christopherdacc/Projet_EEA0601/Compte_rendu/Finale/Présentation_Errard_Daccache.pdf

# Projet : Robot suiveur de ligne

MODULE EEA 0601

TP TRANSDISCIPLINAIRE ANNÉE 2023/2024

1

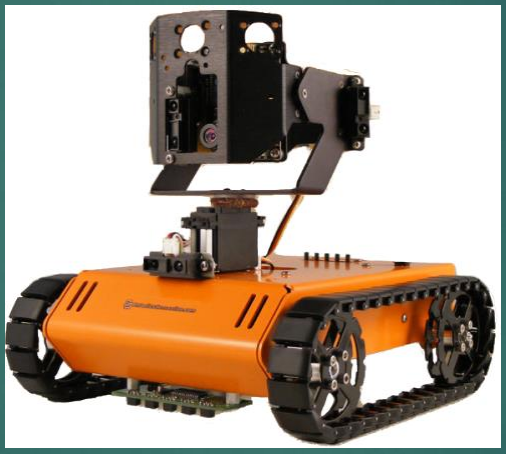
[picture p47: figure]

Sujet : Interface Homme Machine d’un Robot Suiveur de Ligne Réalisé par ERRARD Mathéo et DACCACHE Christopher Enseignants responsables : COLAS Maxime et CARTON David

2

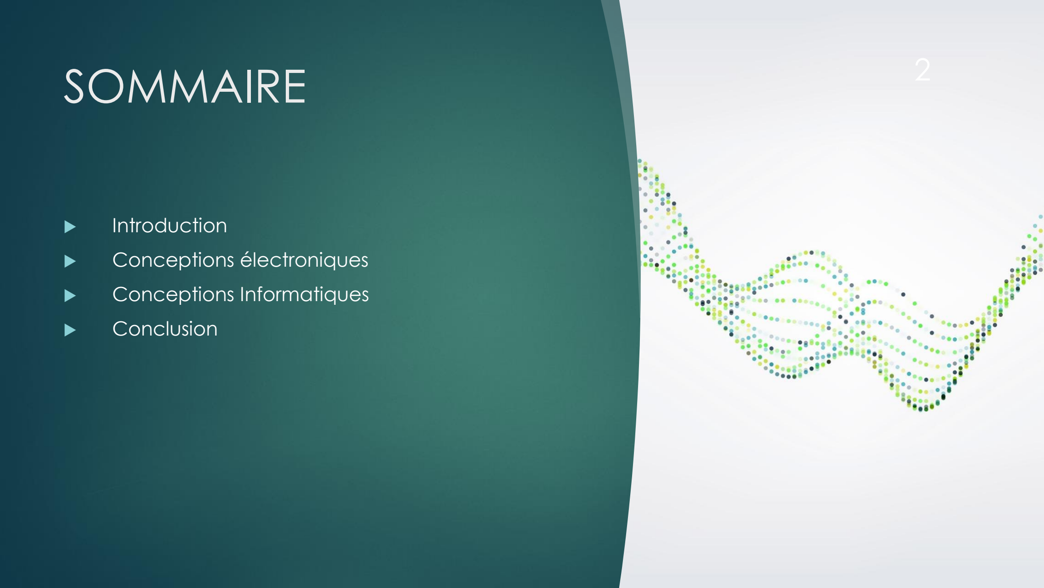
[picture p48: page 2]

SOMMAIRE | Introduction | Conceptions électroniques | Conceptions Informatiques | Conclusion

I. Introduction Cahier des charges Matériel Utilisé
3

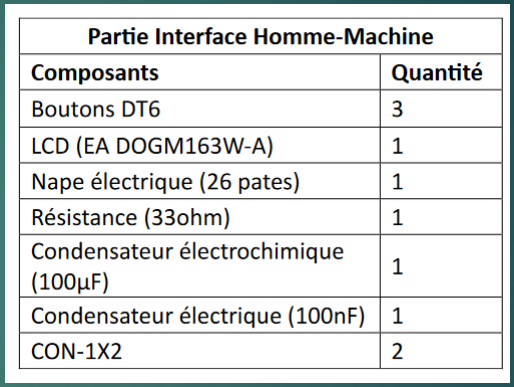
[picture p49: figure]
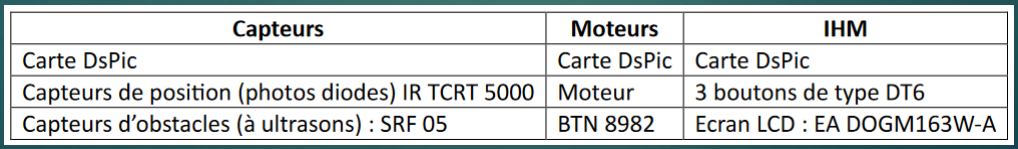
[picture p50: figure]

# I. Introduction Planning

4

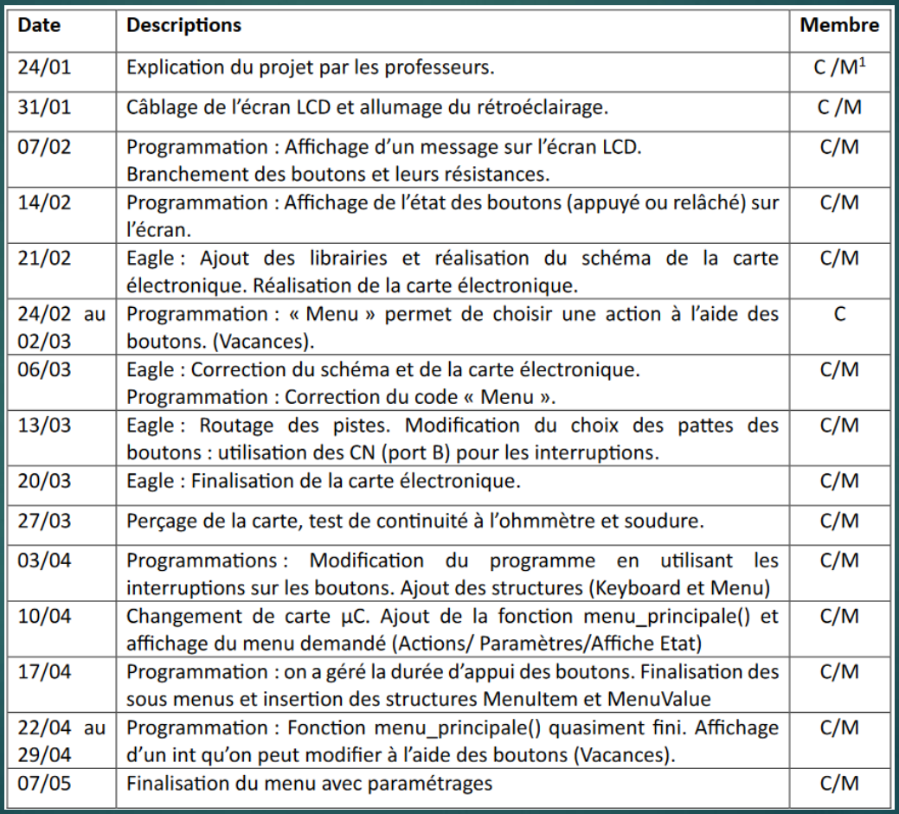
[picture p51: figure]

# II. Conceptions électroniques

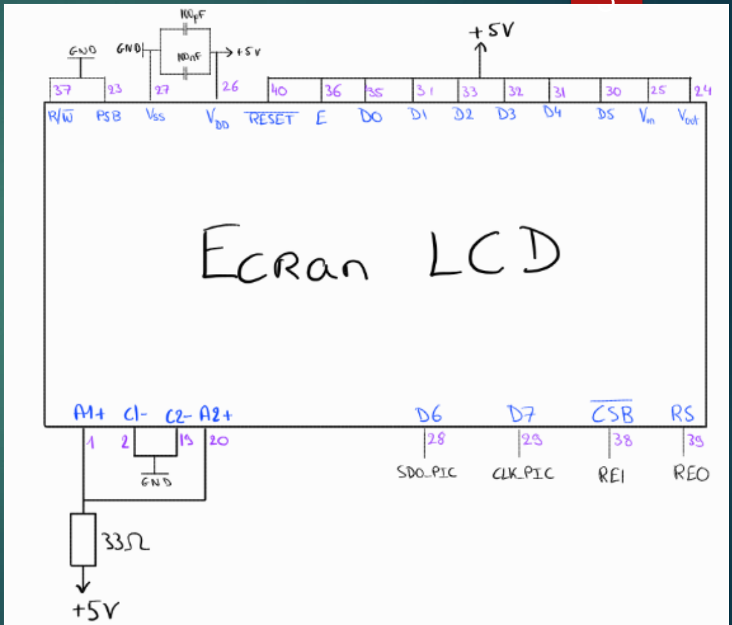
[picture p52: figure]

- Ecran : 22 pins sur 40 d’utilisés
- Résistance : 33Ω
- 2 Capacités : 100µF et 100nF

5

# a) Câblages

# II. Conceptions électroniques

6

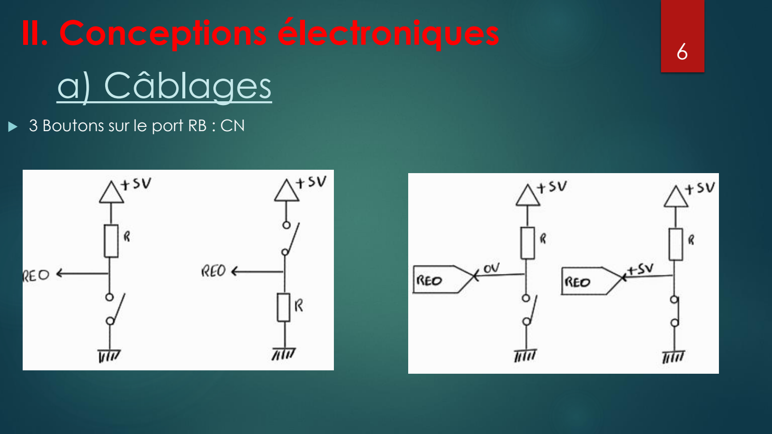
[picture p53: page 6]

- 3 Boutons sur le port

RB : CN

# a) Câblages

# II. Conceptions électroniques

- Schéma électronique
- Carte électronique
- Dimensionnement
- Prévention des perturbations électromagnétiques
- Perçage et soudure

7

# b) Réalisation Carte Électronique

8

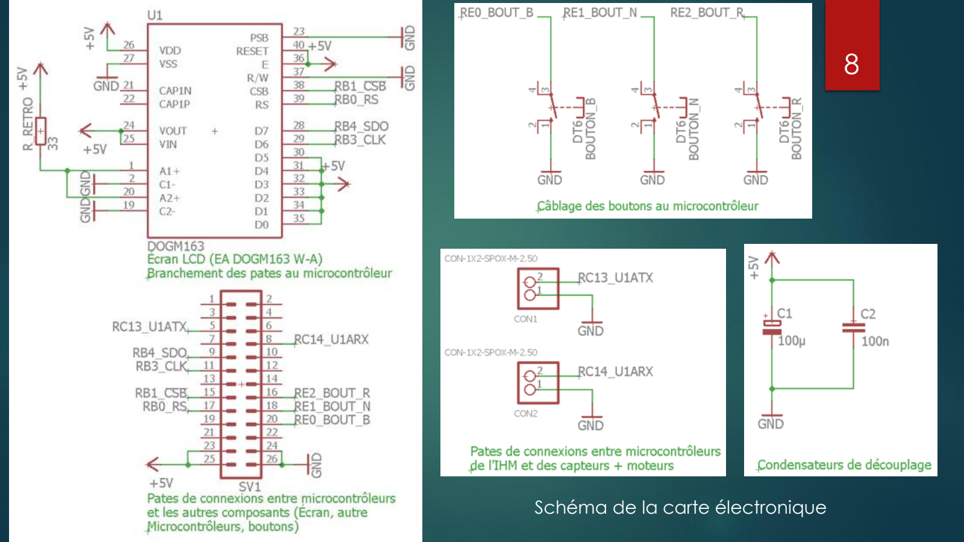
[picture p54: page 8]

Schéma de la carte électronique

9

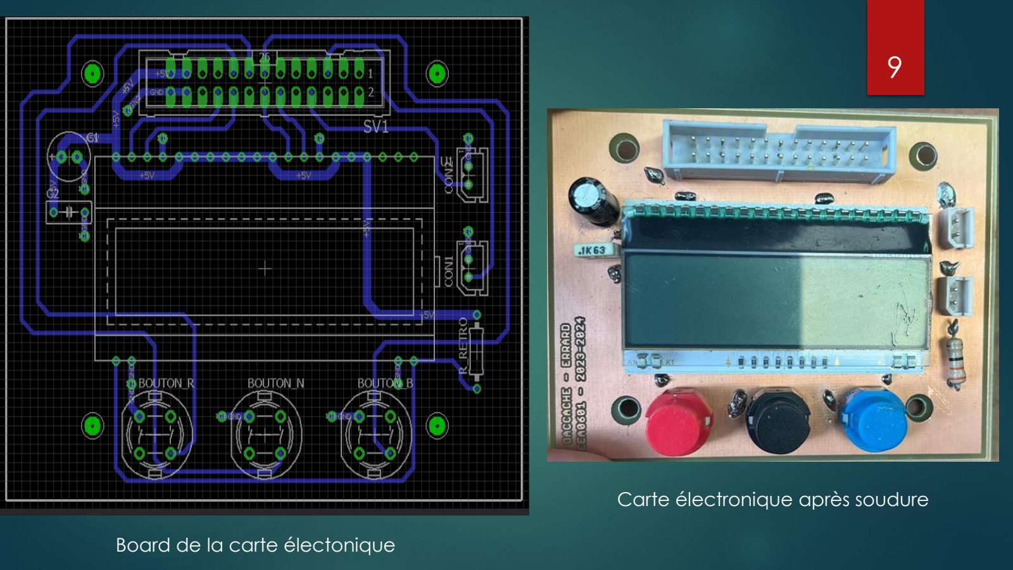
[picture p55: page 9]

Board de la carte électonique

Carte électronique après soudure

# III. Conceptions Informatiques

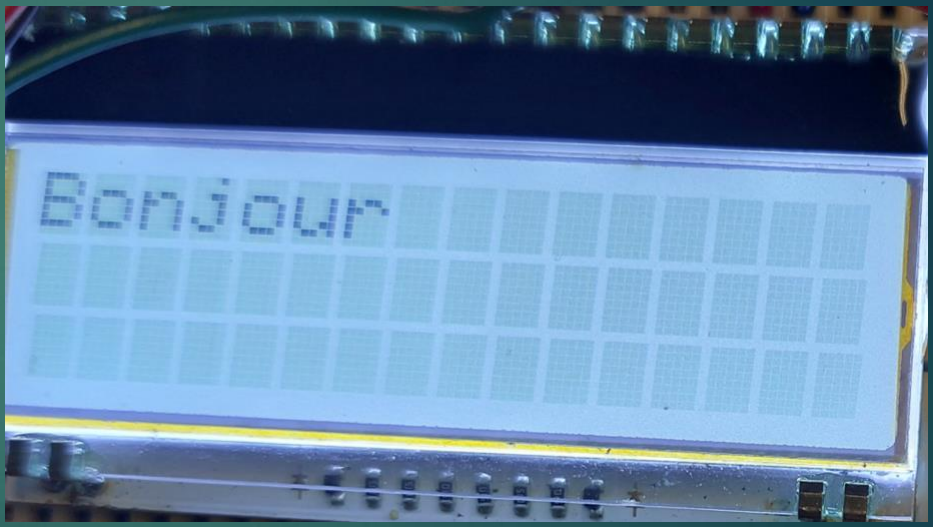
[picture p56: figure]

## - Premier programme simple :

« InitLCD();
LCDDisplayOn();
LCDGoto(0,0);

## LCDWriteStr(« Bonjour"); »

- LCDGoto(X,Y);

## X : nombre de ligne

## Y : Position sur la ligne

10

# a) Affichage et test des boutons

# III. Conceptions Informatiques

- Programmation des boutons : #define BUTTON1_PIN PORTBbits.RB0 #define BUTTON2_PIN PORTBbits.RB1 #define BUTTON3_PIN PORTBbits.RB2

void init_pins() {
TRISBbits.TRISB0 = 1;
TRISBbits.TRISB1 = 1;
TRISBbits.TRISB2 = 1;
CNPU1bits.CN2PUE = 1;
CNPU1bits.CN3PUE = 1;
CNPU1bits.CN4PUE = 1;
}

11

# a) Affichage et test des boutons

do{
while (myKeyboardptr->enterEdge==1) {
LCDGoto(0,0);
LCDWriteStr("Button 1 = 1"); }

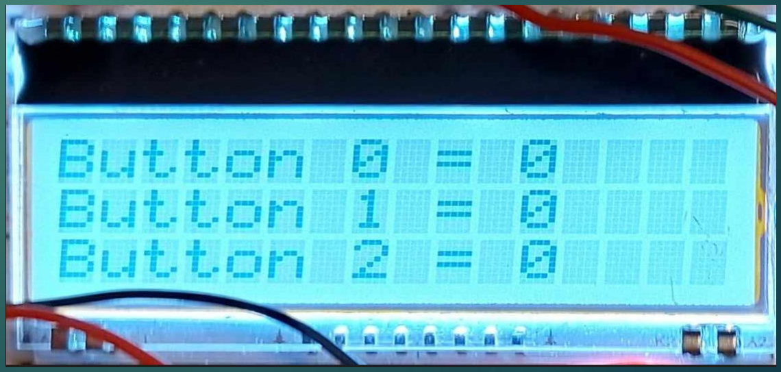
[picture p57: figure]

II

I. Conceptions Informatiques | 12 b) Structure du Menu

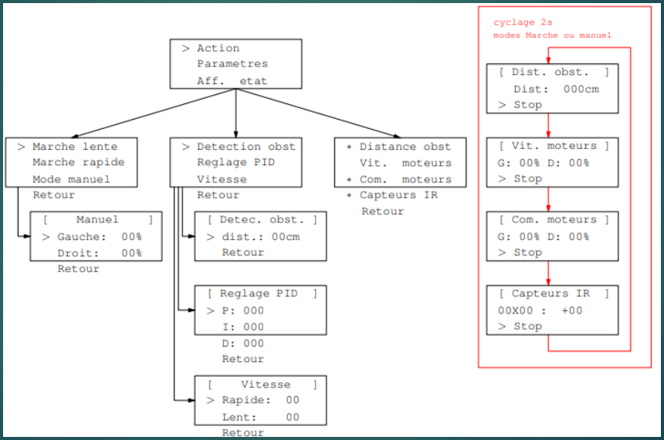
[picture p58: figure]

II

I. Conceptions Informatiques | 13 b) Structure du Menu

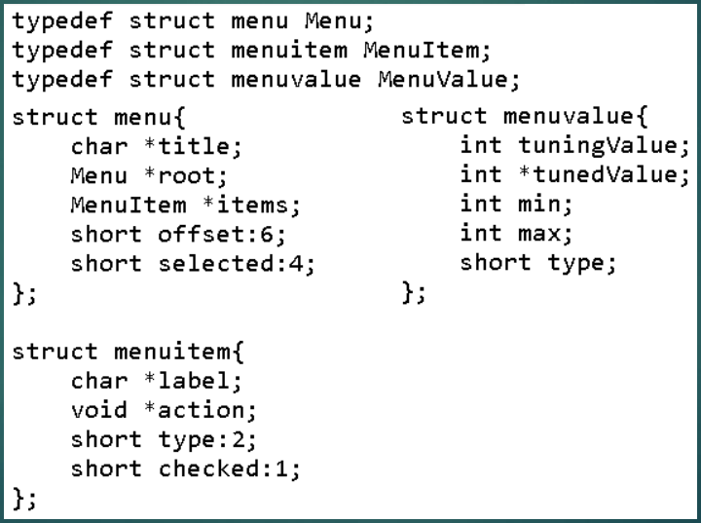
[picture p59: figure]

II

I. Conceptions Informatiques | 14 c) Initialisation du Menu

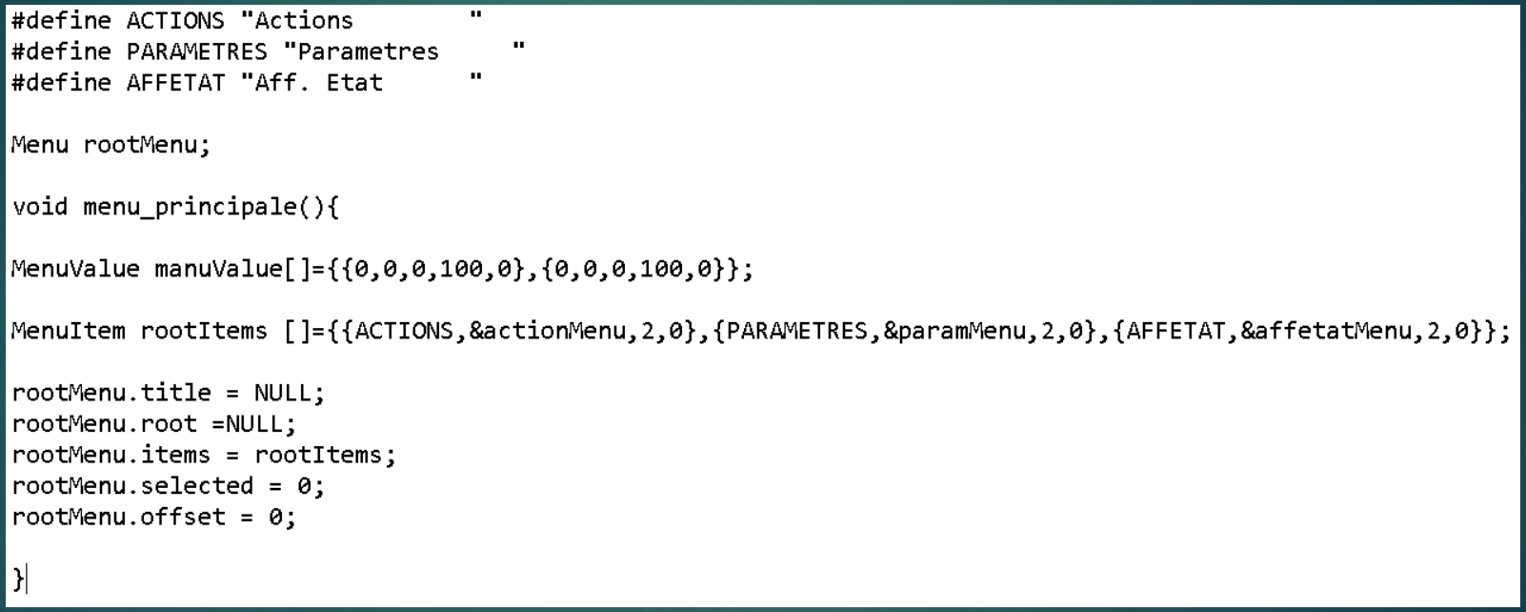
[picture p60: figure]

d | 15 ) Paramètres du Menu

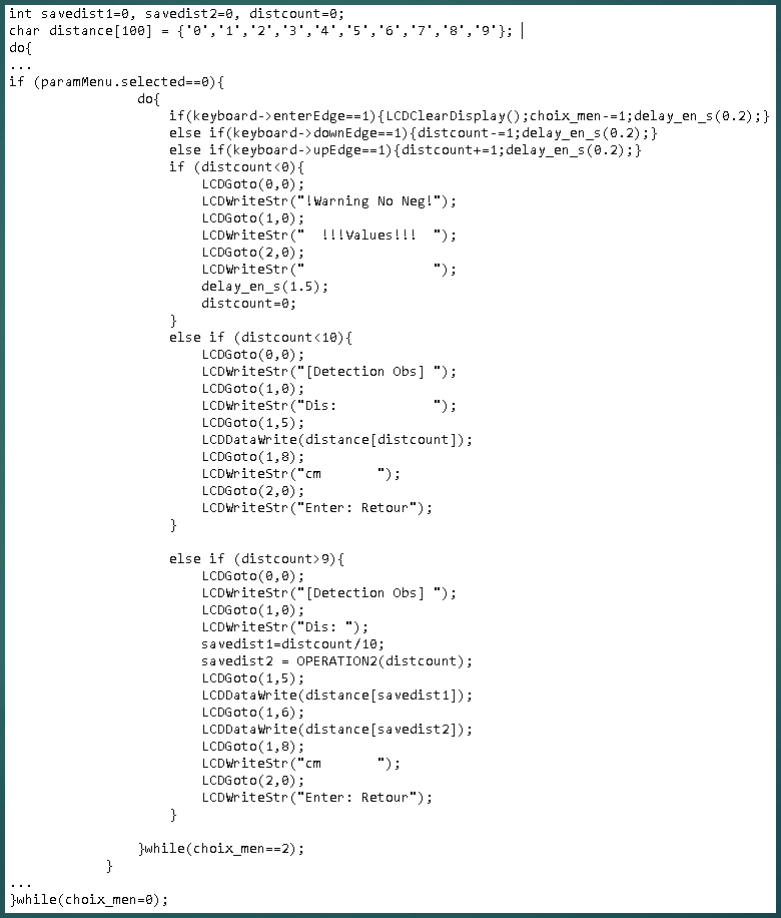
[picture p61: figure]

- Difficultés Solutions Projet finale Conclusion
IV. Conclusion | 16
