christopherdacc/Projet_EEA0601/Carte_eagle/carte_realise/Screenshot_board_updated.PNG

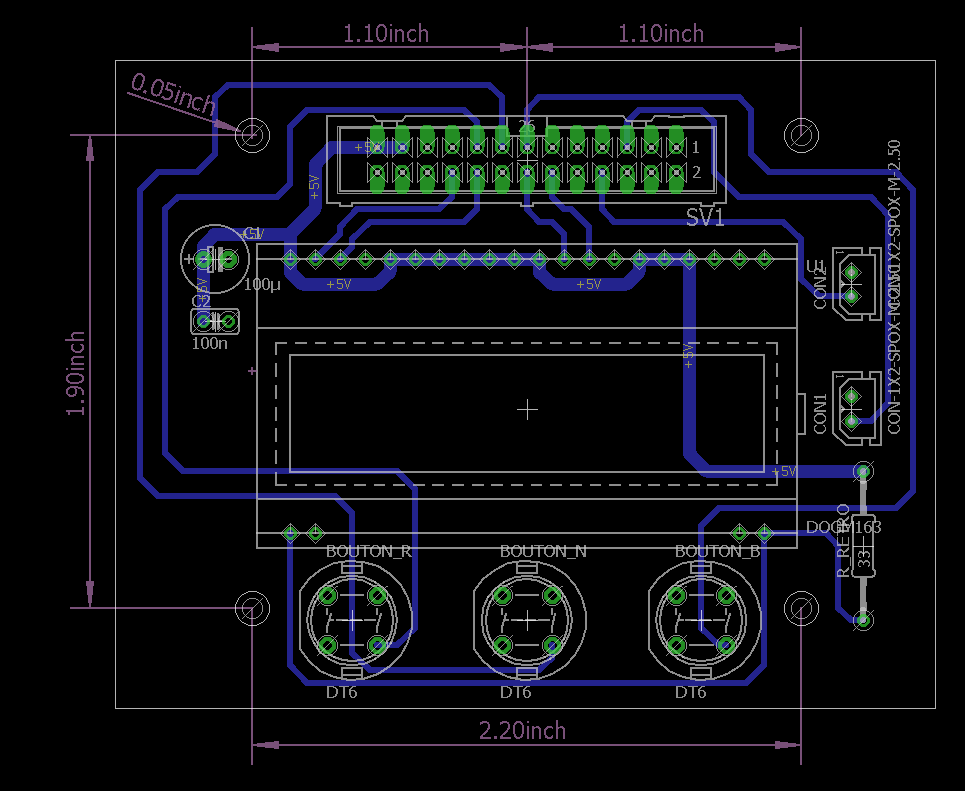
Carte_eagle/carte_realise/Screenshot_board_updated.PNG
