christopherdacc/Projet_EEA0601/Compte_rendu/pics and files/code/correction 1.PNG

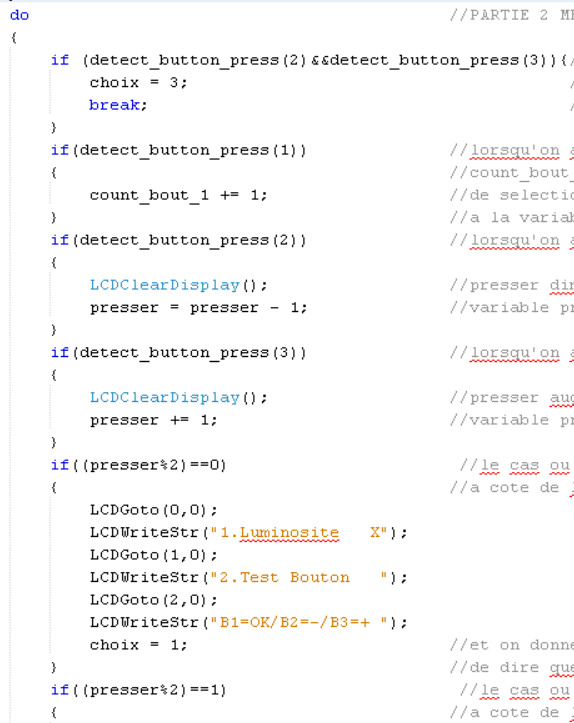
Compte_rendu/pics and files/code/correction 1.PNG
