christopherdacc/Projet_EEA0601/Compte_rendu/pics and files/code/correction 2.PNG

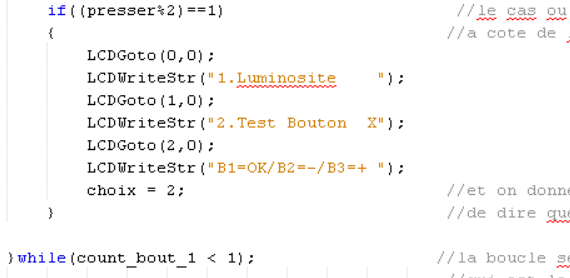
Compte_rendu/pics and files/code/correction 2.PNG
