christopherdacc/Projet_EEA0601/Compte_rendu/pics and files/code/demarage de la fct menu.PNG

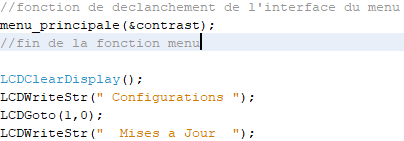
Compte_rendu/pics and files/code/demarage de la fct menu.PNG
