christopherdacc/Projet_EEA0601/Compte_rendu/pics and files/cond de decoup.PNG

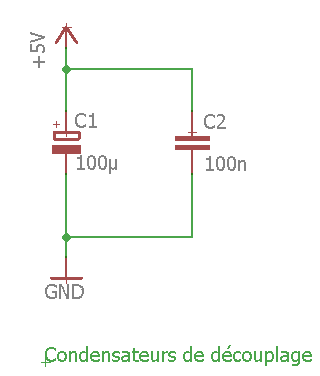
Compte_rendu/pics and files/cond de decoup.PNG
