christopherdacc/Projet_EEA0601/Compte_rendu/pics and files/ecran pins.jpg

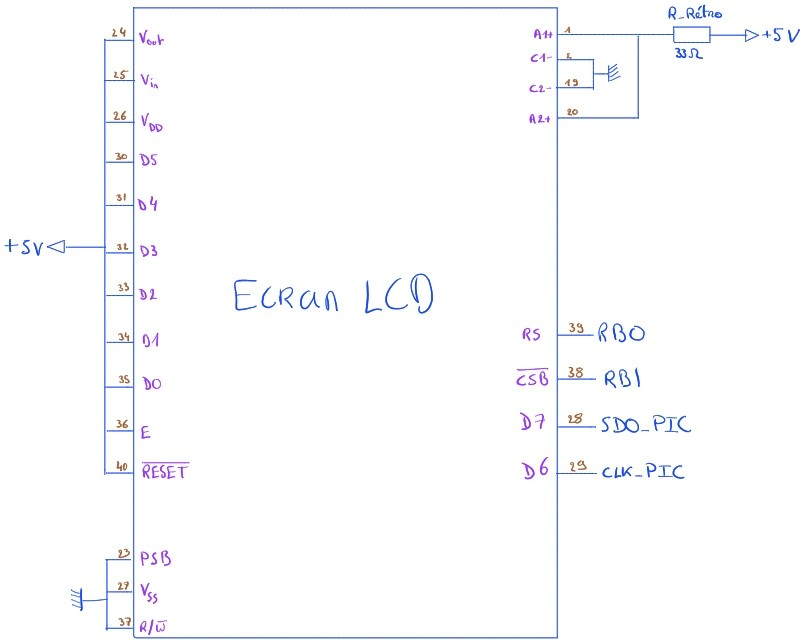
Compte_rendu/pics and files/ecran pins.jpg
