christopherdacc/Projet_EEA0601/Compte_rendu/pics and files/Finale/ecran LCD.PNG

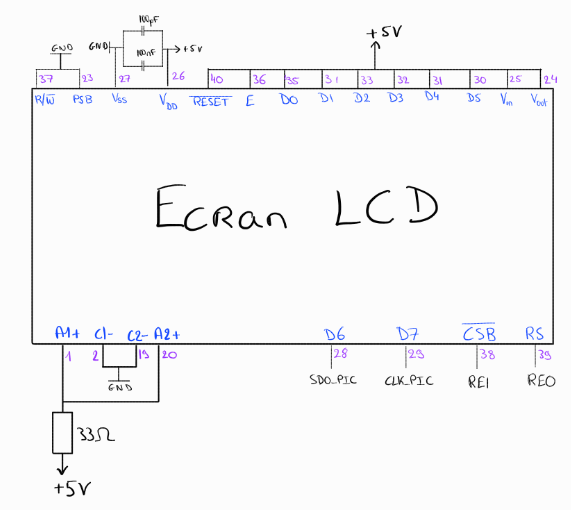
Compte_rendu/pics and files/Finale/ecran LCD.PNG
