christopherdacc/Projet_EEA0601/Compte_rendu/pics and files/Finale/function and header.PNG

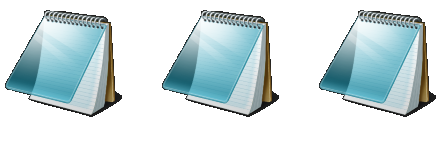
Compte_rendu/pics and files/Finale/function and header.PNG
