christopherdacc/Projet_EEA0601/Compte_rendu/pics and files/Finale/organigramme boutons 1.png

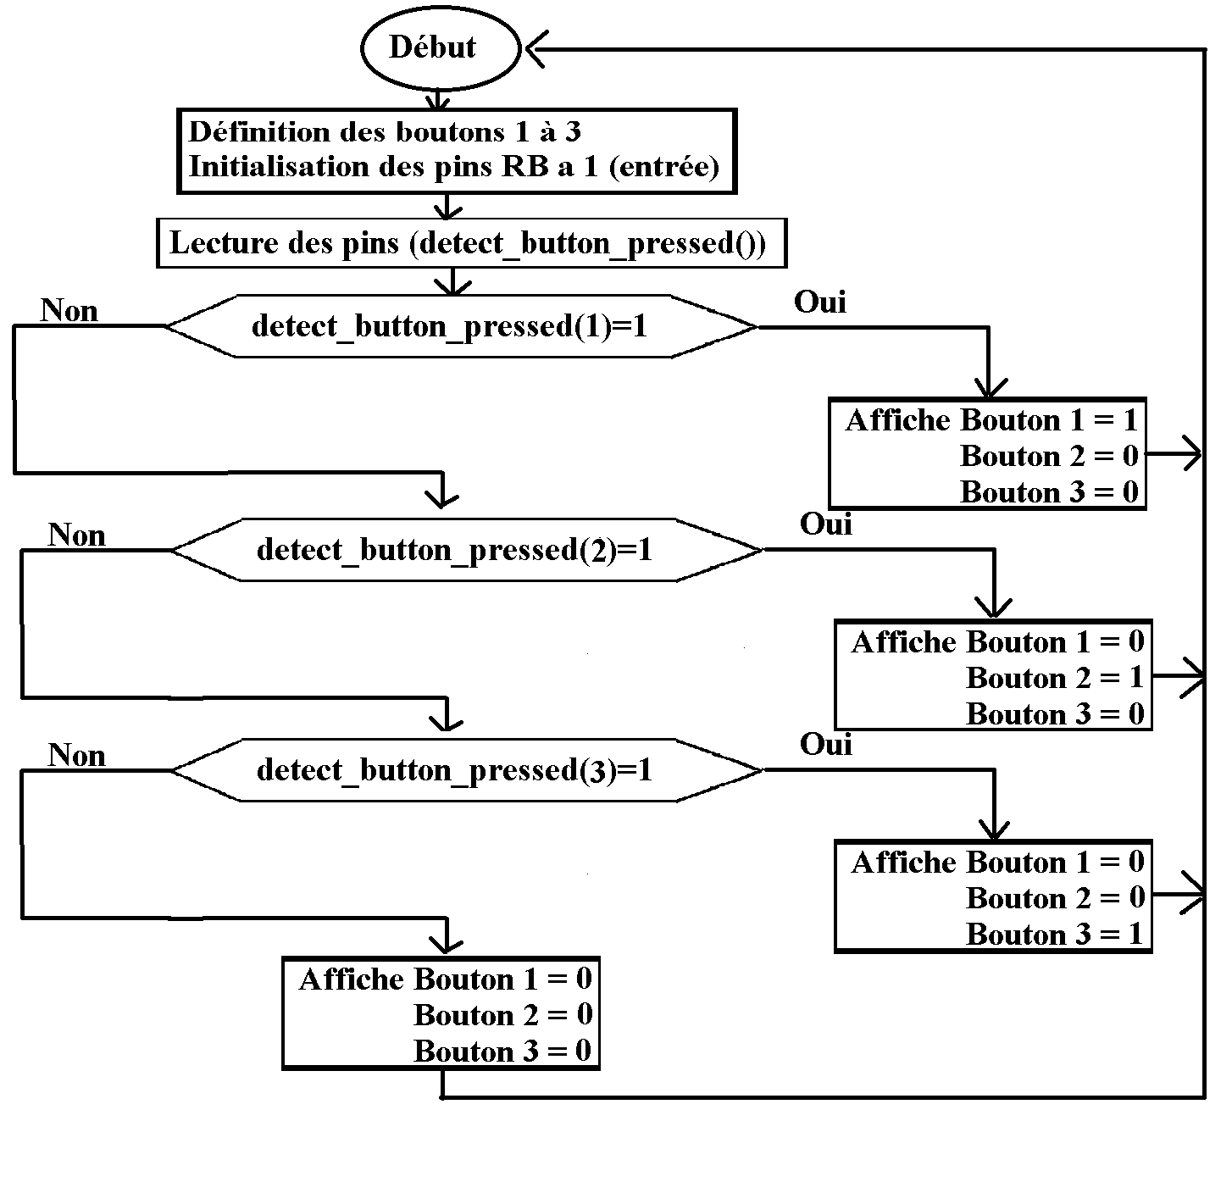
Compte_rendu/pics and files/Finale/organigramme boutons 1.png
