christopherdacc/Projet_EEA0601/Compte_rendu/pics and files/Finale/organigramme Menu.png

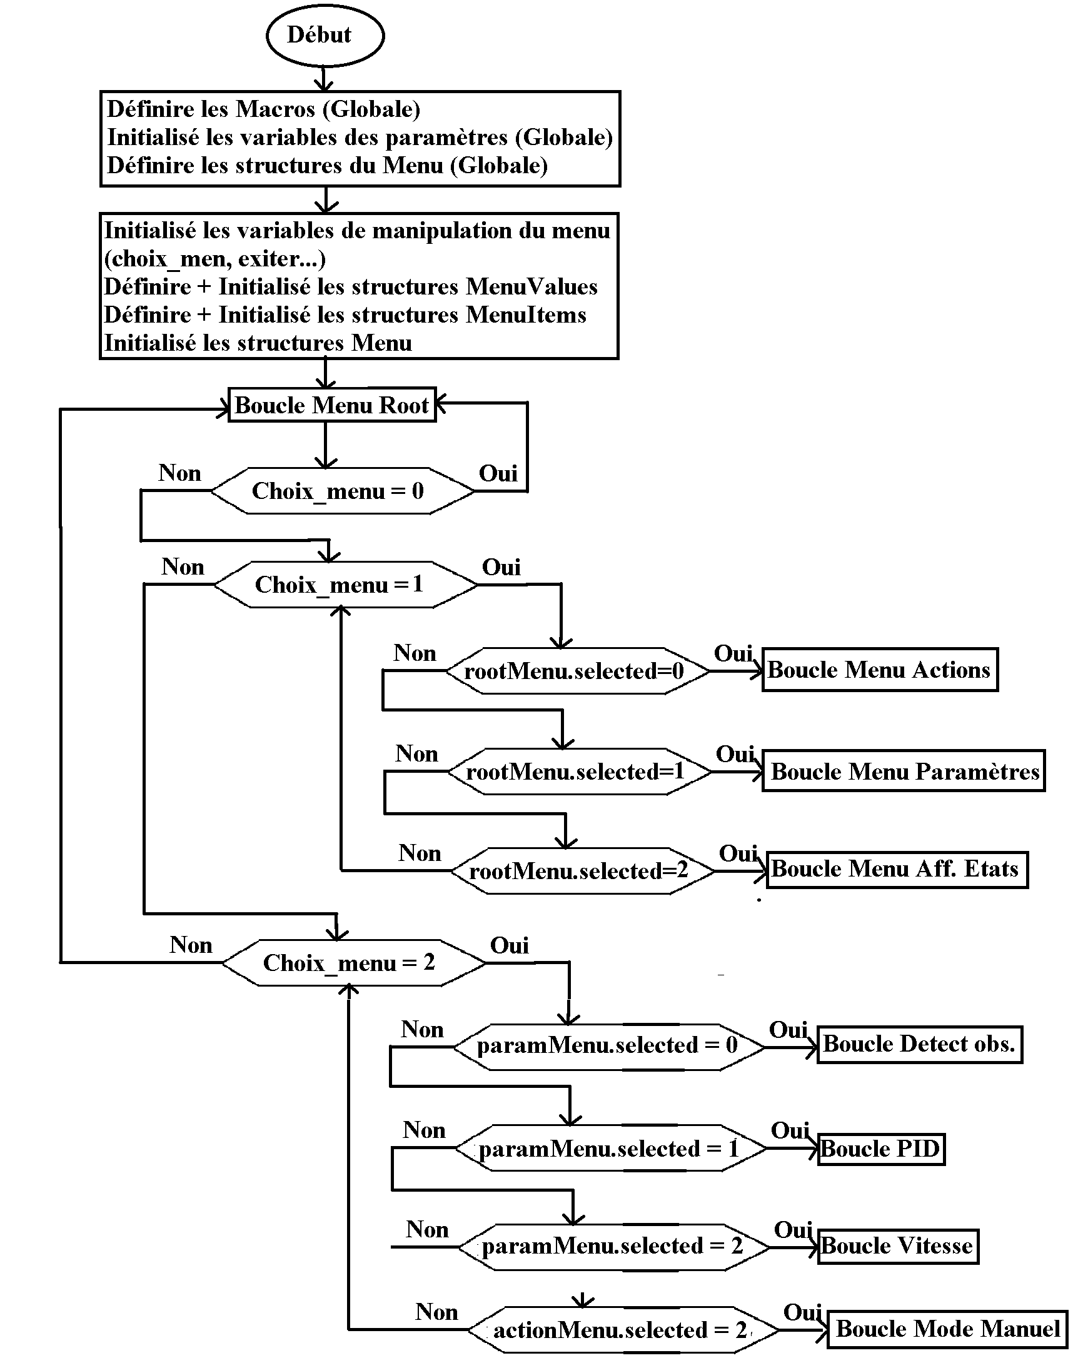
Compte_rendu/pics and files/Finale/organigramme Menu.png
