christopherdacc/Projet_EEA0601/Compte_rendu/pics and files/Finale/structure du menu graphe.PNG

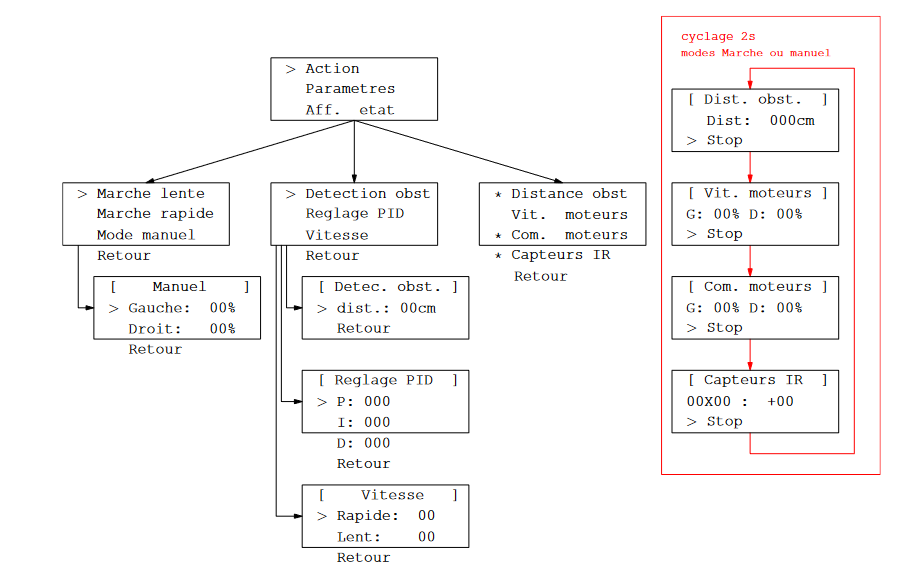
Compte_rendu/pics and files/Finale/structure du menu graphe.PNG
