christopherdacc/Projet_EEA0601/Compte_rendu/Screenshot_20240514_171942_Gallery.jpg

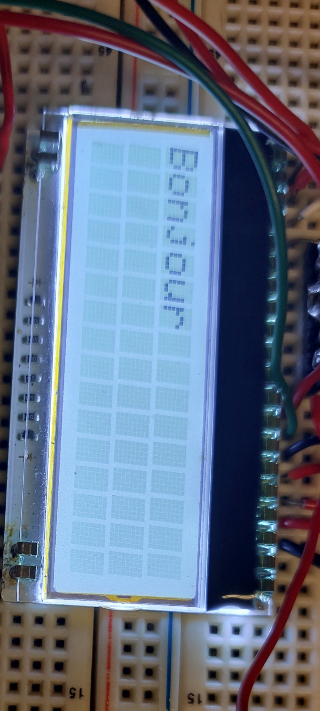
Compte_rendu/Screenshot_20240514_171942_Gallery.jpg
