christopherdacc/Projet_EEA0601/Programmation/Librairies-20240219/periph_ic.h

/***********************************************************
************************************************************
*
* Fichier de configuration et de gestion IC
*
*           D. CARTON, M. COLAS - Mars 2008
*                        V 1.2
************************************************************
***********************************************************/

/***********************************************************
*                      IC7 sur RB4                         *
***********************************************************/

#ifndef IC_H
#define IC_H



#define RISING 3      // définition  fronts
#define FALLING 2     //
#define EVERY 1       //

void IC7InterruptEnable(unsigned int edge);

#endif
